StoneHW-21/-2/Pictures/3927640110.jpg

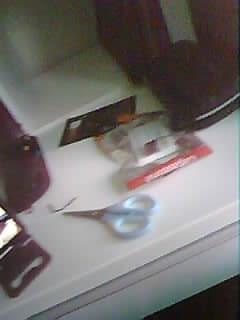
Pictures/3927640110.jpg
